stsepelin/zeppl/docs/reference/J1850-BUS.md

# J1850 bus reference — pinout, decode table, IM simulation

Reference for the V-Rod's SAE J1850 VPW bus: the 12-pin connector map, the
decoded message table (calibrated against real captures), the IM-simulation
protocol, and CRC. Status and roadmap live in [`../ROADMAP.md`](../ROADMAP.md);
the transceiver circuit + build live in [`HARDWARE.md`](HARDWARE.md).

## V-Rod instrument module 12-pin connector pinout

> Physical face map for building a mating quick-connect (cavity positions +
> wire colours): [`../schematics/im_connector_face.svg`](../schematics/im_connector_face.svg).
> Connector is a **Deutsch DTM06-12S** socket (molded marking); the bottom row
> numbering is **inverted** (12,11,10,9,8,7 left→right), verified on the bike.

| Pin | Wire Color | Signal | Type | T-tap Color | ESP32-P4 Connection |
|---|---|---|---|---|---|
| 1 | R/O (Red/Orange) | +12V Battery (constant) | Power | **Blue** | NOT used for cluster power (constant → would drain the battery key-off); switched pin 6 is the source instead |
| 2 | White | High Beam | 12V discrete | Red | → Voltage divider → GPIO input |
| 3 | Violet | Left Turn signal | 12V discrete | Red | → Voltage divider → GPIO input |
| 4 | Brown | Right Turn signal | 12V discrete | Red | → Voltage divider → GPIO input |
| 5 | BK/GN (Black/Green) | Ground | Power | **Blue** | → Common GND |
| 6 | Grey | +12V Ignition (switched) | Power | **Blue** | **cluster power source.** Full path (split point S2): pin 6 → **F1 2A inline in the harness** → signal board terminal (1,3) → row-1 rail (Q2's emitter taps off here) → transit (18,2) → power board → D2 → TVS1 → Mini560 → D4 → board 5V header. The signal board is upstream of D2, so it is fused but **not** reverse-protected. See [`../../firmware/docs/reference/bike-power-injection.md`](../../firmware/docs/reference/bike-power-injection.md) and [`../schematics/bike-power-chain.py`](../schematics/bike-power-chain.py). **⚠ Pin-6 conflict, OPEN:** this same pin is also listed as the sixth divider input (lane G6 "ignition"). Since pin 6 powers the board, G6 can only ever read "on". Options are laid out in [`../phases/phase3-cluster.md`](../phases/phase3-cluster.md); not yet decided. |
| 7 | LGN/V (Light Green/Violet) | **J1850 Data Bus** | Digital bus | Red | → DIY transceiver (RX + TX) |
| 8 | (3-pin sub-connector) | Vehicle Speed Sensor | Pulse | Red | → GPIO input (pulse counter) |
| 9 | GN/Y (Green/Yellow) | Oil Pressure warning | 12V discrete | Red | → Voltage divider → GPIO input |
| 10 | TN (Tan) | Neutral indicator | 12V discrete | Red | → Voltage divider → GPIO input |
| 11 | Y/W (Yellow/White) | Fuel Level sender | Analog resistance (see note) | Red | → ADC pin (GPIO 22 reserved) |
| 12 | O/W (Orange/White) | Accessories | 12V accessory | Red | → Optional |

Discrete-signal polarity (which lines are active-high vs active-low) and the
ultrasonic fuel-sender caveat are in the Phase 3 section of
[`../ROADMAP.md`](../ROADMAP.md).

## IM (instrument module) simulation

### Why it's needed
The V-Rod ECM expects the stock IM to respond on the J1850 bus. Without it:
U1255 DTC (missing response), possible TSSM security lockout.

### How it works
The P4 firmware periodically sends the same J1850 messages the stock IM sends,
via the high-side transceiver (IRLZ44N low-side driver → 2N2907A PNP sourcing
the bus HIGH for dominant). The ECM sees a "live" IM and stays happy.

> **Status (2026-07-24): Steps 1-3 done, on-bike validated.** Capture (Step 1)
> and Replay (Step 2) are live: the fabricated PCB keys the IM keep-alive set on
> the real bus with **0 watchdog faults over 312 sends** (engine-off/on +
> cold-start), stock cluster still attached, **no DTCs** (ROADMAP Phase 2
> Stage 4 + [`../../firmware/docs/rides/stage4-tx-bench-log.md`](../../firmware/docs/rides/stage4-tx-bench-log.md)).
> Step 3's stock-cluster **removal** / U1255 / TSSM checks are the open follow-up.

### Implementation steps

**Step 1 — Capture.** Proxy box passes everything to the stock cluster; log ALL
J1850 traffic for 5+ minutes (ignition on, engine running, riding); filter for
the messages the IM SENDS (not the ECM); document bytes, intervals, CRC.

**Step 2 — Replay.** Program the P4 to send the captured IM messages at the
right intervals via the TX circuit; VPW bit timing via RMT (64/128 µs pulses).

**Step 3 — Test.** Disconnect the stock cluster from the proxy output; run the
IM-simulation firmware; check for U1255 or any other DTCs; test key fob unlock →
start → ride → stop.

**Step 4 — Security handshake (if needed).** If TSSM security fails without the
stock IM: (A) capture + replay the security handshake (complex); (B) Screamin'
Eagle Pro tuner → disable TSSM; (C) keep the stock IM wired in parallel, hidden
under the airbox (fallback).

### CRC
J1850 VPW uses CRC-8 with polynomial 0x1D (CRC-8/SAE-J1850). Implemented in
`firmware/main/engine/j1850/j1850_vpw.c` (host-tested, round-tripped).

## J1850 VPW message decode table

Calibrated against real on-bike captures. The decoder is
`firmware/main/engine/j1850/j1850_parse.c` (host-tested); the DTC codec is `dtc.c`.

```
HEADER             DATA          MEANING
28 1B 10 02 HH LL  HH LL        RPM = (HH<<8 | LL) / 4
48 29 10 02 HH LL  HH LL        Speed: km/h-native raw counts (~117
                                 counts/km-h). speed_mph = speed_raw / 188
                                 (LOCKED Ride 2 — physics + radar, PR #27).
                                 The old /128 was an early bad guess.
48 3B 40 XX         XX           TSSM lever/shift EVENT frame (edge-driven, not
                                 periodic). Mapped in the stationary bike
                                 session 2026-07-24 (one-lever-at-a-time):
                                   bit7 (0x80) = CLUTCH  (toggles with the lever)
                                   bit5 (0x20) = GEAR-SHIFT event (shifter moved)
                                   bit1 (0x02) = clutch-idle / heartbeat marker
                                 Front brake and neutral are NOT on the bus —
                                 both are discrete (brake = lamp switch; neutral
                                 = pin-10 tap, active-low, Ph.6). SUPERSEDES the
                                 earlier "bit5 = brake / bit7 = heartbeat" guess
                                 (that bit5 was the clutch/shift, not the brake).
48 DA 40 39 XX      XX           Turn signals: bitfield, 3=both. On the
                                 2009 VRSCF (verified 2026-07-04):
                                 2=LEFT, 1=RIGHT (swapped vs HarleyDroid)
68 88 10 03         —            Check Engine OFF
68 88 10 83         —            Check Engine ON
A8 3B 10 03 XX      XX           ECM engine-load/throttle (function 3B), NOT
                                 gear (disproven Ride 1). Gear is DERIVED:
                                 argmin |rpm/speed - ratio| over the exact
                                 overall ratios; ~91% correct at divisor 188.
A8 49 10 10 XX      XX           Engine temp: °C = raw - 40 (OBD-style offset).
                                 Confirmed Ride 1: 0x3F(63)=23°C cold,
                                 0x81(129)=89°C warm. (No-offset read 40°C high.)
A8 69 10 06 HH LL  HH LL        Odometer: 1 tick = 0.4 meters
A8 83 10 0A HH LL  HH LL        Fuel consumption ticks: ~0.000309 L/tick
                                 (ml_per_tick=0.309, calibrated Ride 2 fill-up;
                                 supersedes the 0.000040 placeholder). Economy/range.
A8 83 61 12 DX      DX           Fuel gauge 0-6 — IM-ORIGINATED. Fuel LEVEL +
                                 low-fuel are NOT bus-decoded and likely
                                 disappear with the stock IM.
48 92 40 XX YY YY   XX YY YY     IMMOBILISER / security "key" lamp (CONFIRMED
68 93 60 XX YY YY   XX YY YY     on-bike 2026-07-24; decoded in j1850_parse.c ->
                                 the P4 key icon, verified against the stock
                                 cluster). Paired 40/60 sources. At key-on:
                                 data[3]=0xAA ("AA FF FF", not authenticated ->
                                 key lamp ON) for ~4 s, then data[3]=0x2A
                                 ("2A 00 00", authenticated -> lamp OFF).
                                 State bit = data[3] bit7. 48 92 40 is used.
28 FF 10 01 XX      XX           STATUS bitfield. bit0 (0x01) = KILL SWITCH
                                 (1 = STOP, 0 = RUN) — CONFIRMED on-bike
                                 2026-07-24 by toggling the run/stop switch
                                 (0x07<->0x06). Bits 1-2 stay set while
                                 stationary (engine off AND idling) — not oil;
                                 likely clear only when moving (ABS/road status),
                                 untested on the stand. OIL PRESSURE is NOT on
                                 the bus (it's the discrete pin-9 tap, Ph.6).
                                 Left undecoded (no kill-switch cluster icon).
```

Still-undecoded headers are catalogued in
[`../../firmware/docs/reference/j1850-undecoded-frames.md`](../../firmware/docs/reference/j1850-undecoded-frames.md).

### Diagnostic trouble codes (DTCs)
The HD J1850 read/clear protocol (request/response bytes, per-module addresses)
and the on-bike validation are in
[`../../firmware/docs/reference/dtc-read-probe.md`](../../firmware/docs/reference/dtc-read-probe.md);
the codec is `firmware/main/engine/j1850/dtc.c` (host-tested).
