stsepelin/zeppl/firmware/docs/captures/SESSION-2026-07-04.md

# J1850 capture session — 2026-07-04 (first live bike sniff)

2009 VRSCF Muscle, RX-only sniffer through the proxy box, stock cluster
in place. First on-bike Stage 2 session.

> **RESOLVED (2026-07-04): the bus is standard VPW; there is no
> inversion.** The `RX_INVERT` flag was masking the 500 ns hardware
> glitch filter, which dropped the slow recessive (dominant->idle)
> falling edge. Three independent sources agree the bus idles LOW /
> dominant HIGH: (1) bare-bus DMM (ESP disconnected) reads idle ~0.3 V;
> (2) an invert-off raw dump on short leads shows `raw1 low 41 s` (idle
> LOW) then `raw2 HIGH 194 us` (SOF HIGH); (3) with the glitch filter
> off, decode is clean WITHOUT the invert flag — same-level=0, 0 bad
> CRC, the best capture yet. `RX_INVERT` and the low-side TX have both
> been removed. **TX is HIGH-side** (original `j1850_tx.svg`, PNP +
> 2N2907A). See the glitch-window sweep below.

## Root cause: the glitch filter ate the recessive edge (not inversion)

Pulse widths came back textbook VPW (64 / 128 / 200 us) but the decoder
saw 0 frames with correct polarity, and only decoded with
`CONFIG_VROD_J1850_RX_INVERT=y`. That was first read as bus inversion;
the bare-bus DMM (idle LOW) contradicted it. The real cause: the P4
hardware flex glitch filter delays the filtered edge relative to the
ISR's `gpio_get_level()` read, so the recessive falling edge is
recorded at the wrong level — it shows up as over-long HIGH pulses that
break frames and make idle gaps look HIGH. Under invert those long-HIGH
glitches became passive pulses that ended frames cleanly, which is why
the flag "worked."

**Glitch-window sweep (engine running, idle + throttle blips, 6 passes):**

| filter window | frames decoded | bad CRC |
|---|---|---|
| **0 ns (off)** | **125 / 208 / 213 per 9 s** | **0** |
| 400 ns | 0 | — |
| 800 ns | 0 | — |
| 1200 ns | 0 | — |
| 1600 ns | 0 | — |

Only the filter-off window decodes — a hard cliff, not a gradient (400 ns
breaks it as completely as 1600 ns), which is the signature of the
edge-vs-level-read delay, not slow-edge eating. The P4 flex filter also
tops out at 1600 ns (64-tick field on the 40 MHz XTAL; 800 ns on the
default 80 MHz clock), so the 1-5 us some notes imagined was never
reachable. **Tuned default: `CONFIG_VROD_J1850_GLITCH_NS=0`.** Real
noise immunity for the Phase 3 permanent build must come from RX
hysteresis (a comparator front end), not this filter. A candidate ISR
fix — infer the level by toggling instead of reading the pin — would
sidestep the delay race and let a filter coexist; deferred, not yet
tried.

## Captures

| File | Bike state | Notes |
|---|---|---|
| `2026-07-04-inverted.log` | key ON, engine OFF, **neutral**, **high-beam bulb removed**, signals off, stationary | ignition-on baseline; also contains the inversion-discovery raw pulse dump at the top. ~232 frames, ~3% bad CRC. |

## Ignition-on baseline (engine off) — what broadcasts

Bus is sparse at key-on; only these repeat, ~2 s cadence:

- `29 FE 40 ..` / `29 FE 60 ..`  — steady pair
- `68 FF 40 03 D8` / `68 FF 60 03 AD` — steady pair

None match our ECM-oriented decode table (`28 1B`, `48 29`, `A8 ..`) —
these are **IM-originated keep-alive**, the Stage 4 replay candidates.

One-shots seen at power-up: `48 92 40 2A`, `68 93 60 2A`, `29 81 60`,
`68 E0 B0`, and one `48 DA 40 39 00 70` (turn-signal header, value 00 =
off — matches the decode table).

Remember: this baseline has **neutral = engaged** and **beam bulb out**
baked in. Anything that reads those states is at its neutral/beam-off
value here.

## Decoded so far (engine off)

**Turn signals — `48 DA 40 39 XX`** (via TSSM, a bus node). `XX` is a
2-bit field, blinks between the value and `00`:

| XX | meaning | CRC byte |
|----|---|---|
| 00 | off | 70 |
| 02 | **left** | 4A |
| 01 | **right** | 6D |
| 03 | both / hazards (= 01\|02) | 57 |

Note: **left/right are swapped vs the HarleyDroid table** (it says
1=left, 2=right; this bike is 2=left, 1=right). Verified by test order
(left tested first → 02). Our CRC-8 matched every frame.

**Beam, neutral, oil are NOT on the bus.** Toggling high beam and
shifting out of neutral produced zero change in J1850 traffic. On the
V-Rod these are **discrete 12 V wires to the IM** — pin 2 White = high
beam, pin 10 Tan = neutral, pin 9 GN/Y = oil pressure — read locally by
the IM, not broadcast. We tap them directly via voltage dividers in
Phase 3. (Oil light ON at engine-off is normal: no oil pressure with
the engine stopped → pressure switch closed → lamp on; it extinguishes
once the engine builds pressure. Confirms the oil signal works.)

## Decoded — engine running (kill switch RUN woke the ECM)

All validated against live behaviour:

- **RPM — `28 1B 10 02 HH LL`**, `(HH<<8|LL)/4`. Confirmed: idle ~1300,
  tracked a clean sustained rev to **4125 rpm** and back, sampled ~15/s
  (66 ms interval, fast enough to drive a tach). Session max 4684.
- **Engine temp — `A8 49 10 10 XX`** — **units UNRESOLVED, PROVISIONAL.**
  The raw byte climbed `0x3E..0x48` (62..72) as it warmed, but the **stock
  cluster shows NO temperature**, so there is no dial to validate against —
  the earlier "raw = °C" was a plausibility guess, not confirmed. Three
  candidates all fit the observed climb: raw°C (62..72°C), raw°F (~17..22°C),
  or `raw-40=°C` (22..32°C). HarleyDroid's wiki documents `xx = °C + 40`
  (i.e. `raw-40`), with a conflicting source saying °F — a HINT only (its
  turn-signal bits were wrong too). **Resolve with a two-point capture**
  (below): raw byte at cold (~ambient) and fully warm (~90-100°C) fixes
  scale + offset unambiguously. The firmware keeps raw-as-°C provisionally
  and logs the raw byte (`temp:` line).
- **Gear — `A8 3B 10 03 XX`**, `00` = neutral (bits 1,3,7,15,31,63 →
  gears 1-6 per table; only neutral seen on the stand).
- **Check engine — `68 88 10 03`** = OFF (0x83 would be ON).
- **Fuel consumption — `A8 83 10 0A HH LL`** present (88 frames, ever-
  incrementing counter) — this is the tick stream for the fuel-computer
  fallback to the ultrasonic sender (see roadmap Phase 3 caveat).
- **Speed — `48 29 10 02`** header confirmed present (reads 0 on the
  stand). **Units settled: mph-native** — this is a US-market bike, the
  stock cluster reads miles, so the ECM value is mph-based; km/h is a
  DISPLAY-layer conversion, not decode. `vehicle_data.speed_mph` is now
  mph-canonical (the sim producer converts to mph; the display does
  mph→km/h only in metric mode). **Magnitude still provisional**: the
  `/DIV` scale (128 guess) needs a ride — the firmware logs the native
  decoded speed (`speed:` line) to compare against the stock speedometer
  read in its native miles (mechanically driven off this same bus).

## IM keep-alive set (Stage 4 replay candidates)

Steady ~2 s cadence, single payload, present with the stock cluster
connected — the messages the P4 must emit to impersonate the IM:

| Header | payload | interval |
|---|---|---|
| `68 FF 40` | `03 D8` | ~2.0 s |
| `68 FF 60` | `03 AD` | ~2.0 s |
| `29 FE 40` | `01 64` | ~2.0 s |
| `29 FE 60` | `01 11` | ~2.0 s |

(Plus `C8 88 10`, `C8 89 60`, `E8 89 60`, `68 FF 10` — ECM/diagnostic
broadcasts, ~2-6 s. Confirm which are IM- vs ECM-originated by watching
what disappears when the stock cluster is unplugged — that's a Stage 4
test, not done yet.)

Overall: 5177 frames across all captures, ~2% bad CRC (healthy, even at
5k rpm). Full breakdown: `tools/j1850_report.py firmware/docs/captures/*.log`.

## Ride / engine session agenda (next, done safely)

> These captures now run **laptop-free**: build with `CONFIG_VROD_RIDE_LOG=y`,
> hit REC on the BENCH screen, ride, hit STOP, then power off and pull the
> microSD card. The log persists native speed, the raw temp byte, and gear
> raw+decoded per frame (see Stage 3.5 in the Phase 2 plan). Needs the ESP on
> bike power (switched +12V via the buck), NOT USB. Run
> `tools/j1850_report.py /sdcard/ride_NNN.log` afterward.

- **Road speed** `48 29 10 02` — units settled (mph-native); confirm the
  `/DIV` magnitude by comparing the logged native speed (`speed:` line)
  against the STOCK SPEEDOMETER read in its native miles (ignore the km/h
  sticker — the mechanism reads mph) at steady 30 / 50 / 70. The stock
  speedo may read ~5-10% optimistic, so this is a coarse check; correct
  DIV if off by a clean factor. (No onboard GPS.)
- **All six gears** `A8 3B 10 03 XX` — only neutral (00) seen parked;
  shift up through the box to log 1st-6th and confirm the table's
  `1,3,7,15,31,63` per-gear values.
- **Two-point temperature** `A8 49 10 10` — record the RAW byte
  (`temp:` line) at TWO known temps: (1) cold engine sat overnight ≈
  ambient (note the ambient), (2) fully warmed ≈ 90-100 °C. Two points fix
  scale AND offset, choosing between raw°C / raw°F / `raw-40=°C`. No dial
  reference exists (stock cluster shows no temp), so this capture is the
  only way to resolve it.
- Anything else speed-dependent we haven't seen at rest.

## Other open items
- **Bus polarity + TX topology — RESOLVED (see the banner at the top).**
  Standard VPW, idle LOW (~0 V), dominant HIGH (~7 V) → **high-side TX**
  (original `j1850_tx.svg`, PNP + 2N2907A). `RX_INVERT` and the low-side
  `j1850_transceiver.svg` are removed. The old "inversion" was the
  500 ns glitch filter dropping the recessive edge; filter now defaults
  off (`CONFIG_VROD_J1850_GLITCH_NS=0`).
- **RX noise immunity (Phase 3):** with the hardware filter unusable,
  vibration/ignition-noise rejection on the permanent harness needs RX
  hysteresis (comparator front end). Optionally revisit the toggle-based
  ISR level capture, which would let a small filter coexist.
- **IM- vs ECM-originated split** — confirm by unplugging the stock
  cluster and seeing which keep-alives vanish (Stage 4).
