stsepelin/zeppl/docs/adr/README.md

# Architecture Decision Records

Short, dated records of significant architecture decisions — the *why* behind a
structural direction, kept next to the code so the reasoning survives. One file
per decision, numbered.

| # | Decision | Status |
|---|---|---|
| [0001](0001-engine-display-split.md) | Engine / connectivity / display separation (contract-first; CAN+DBC interop; defer the board split) | Proposed |

New ADR: copy the shape of an existing one — context, decision, consequences,
and (if it implies work) a phased plan + open questions.
