stsepelin/zeppl/firmware/main/assets/boot.gif

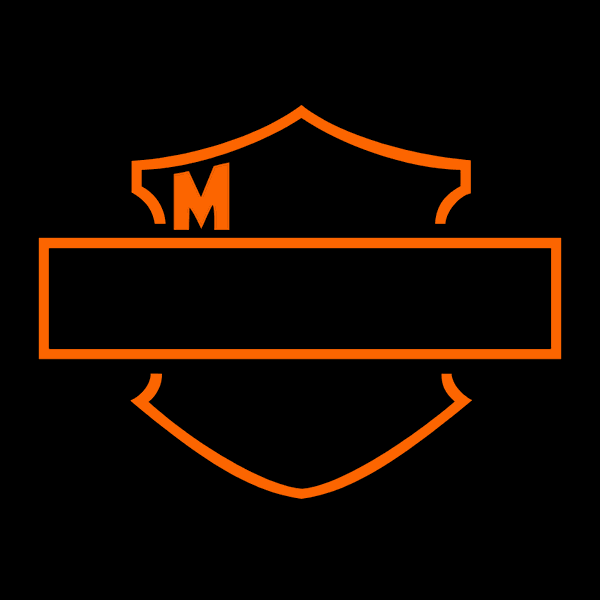
firmware/main/assets/boot.gif
