stsepelin/zeppl/hardware/enclosure/bezel.png

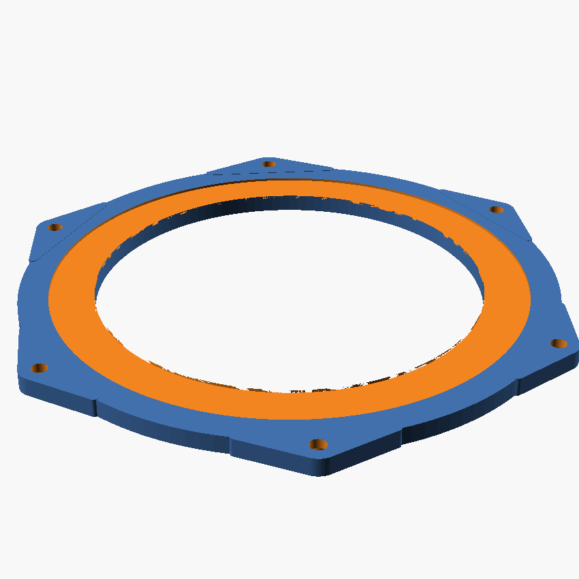
hardware/enclosure/bezel.png
