stsepelin/zeppl/hardware/enclosure/bezel_ear_closeup.png

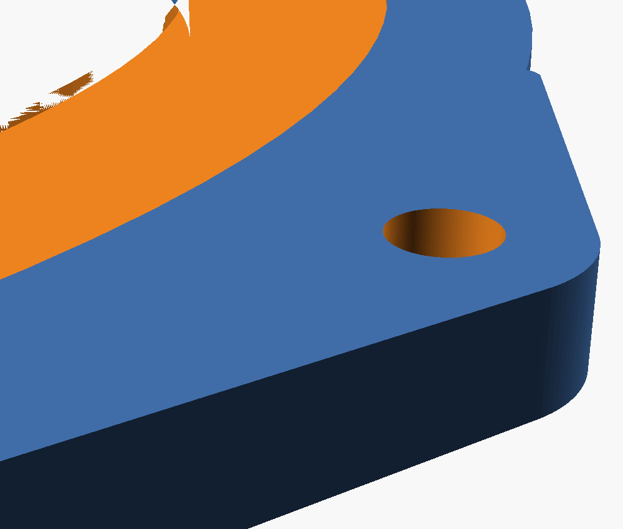
hardware/enclosure/bezel_ear_closeup.png
