stsepelin/zeppl/hardware/enclosure/cable_hole_view.png

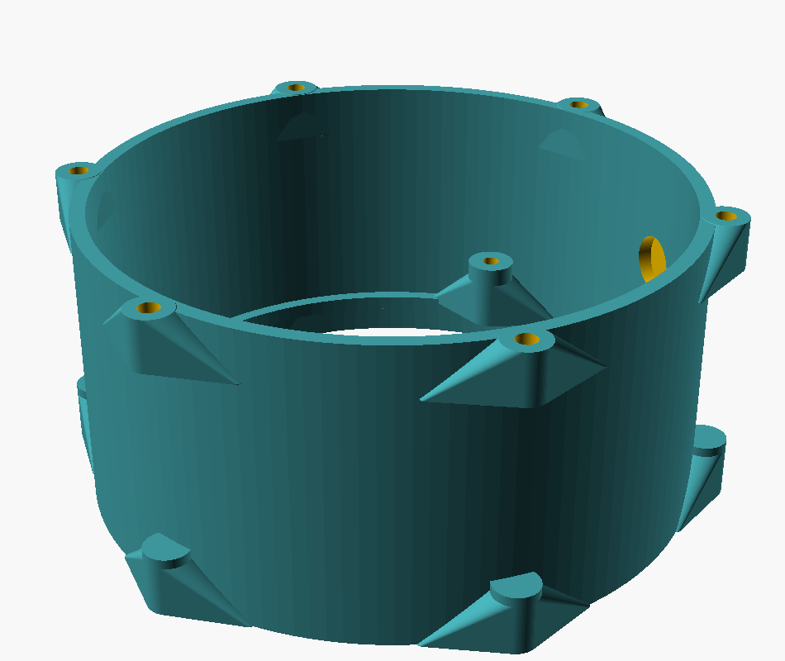
hardware/enclosure/cable_hole_view.png
