stsepelin/zeppl/hardware/enclosure/perimeter_boss_closeup.png

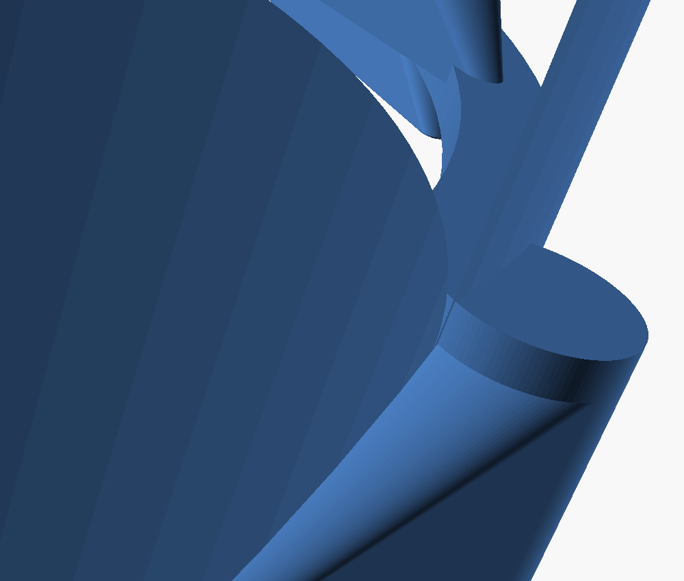
hardware/enclosure/perimeter_boss_closeup.png
