stsepelin/zeppl/hardware/enclosure/rear_case.png

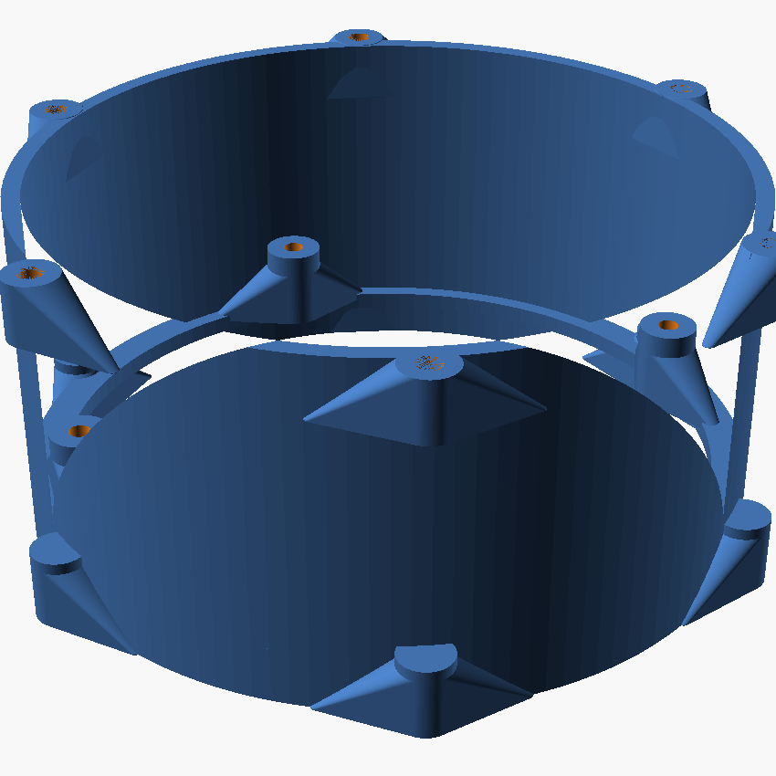
hardware/enclosure/rear_case.png
