stsepelin/zeppl/hardware/enclosure/rear_cover.png

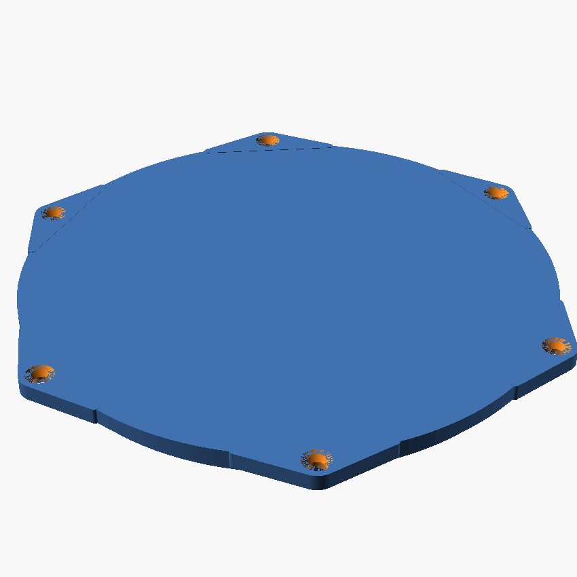
hardware/enclosure/rear_cover.png
