stsepelin/zeppl/hardware/enclosure/section.png

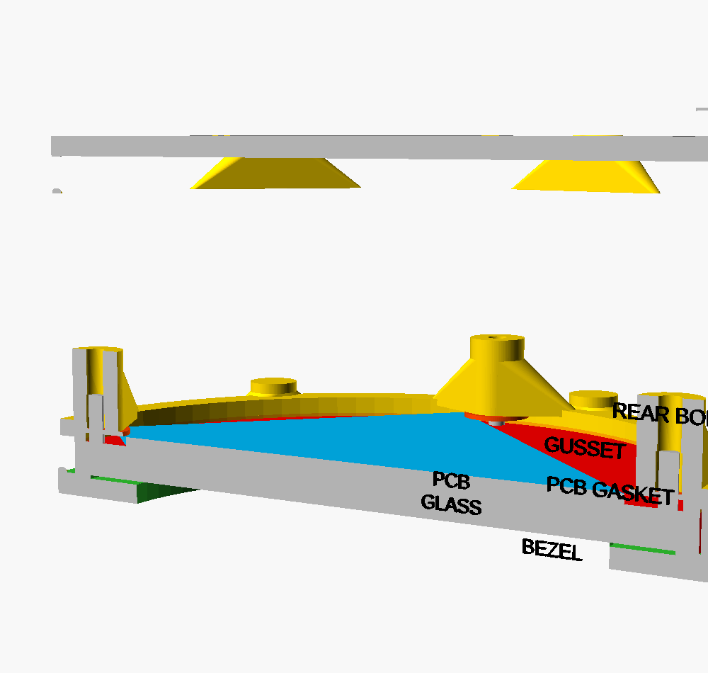
hardware/enclosure/section.png
