stsepelin/zeppl/hardware/enclosure/standoff_closeup.png

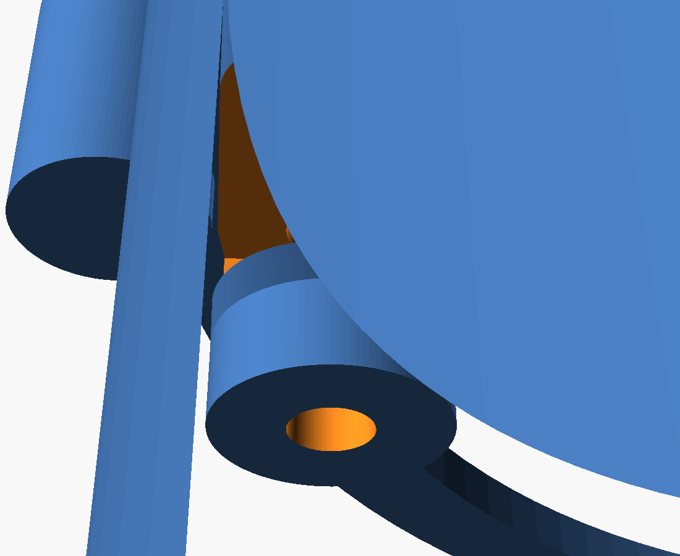
hardware/enclosure/standoff_closeup.png
