stsepelin/zeppl/hardware/enclosure/assembly.png

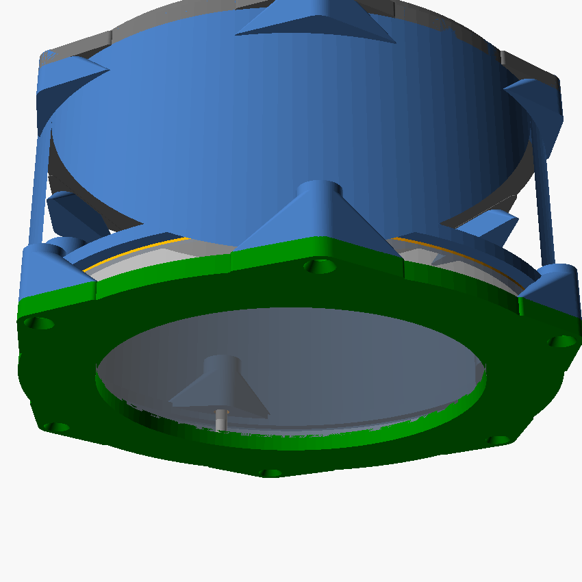
hardware/enclosure/assembly.png
