stsepelin/zeppl/hardware/enclosure/calibration_base.png

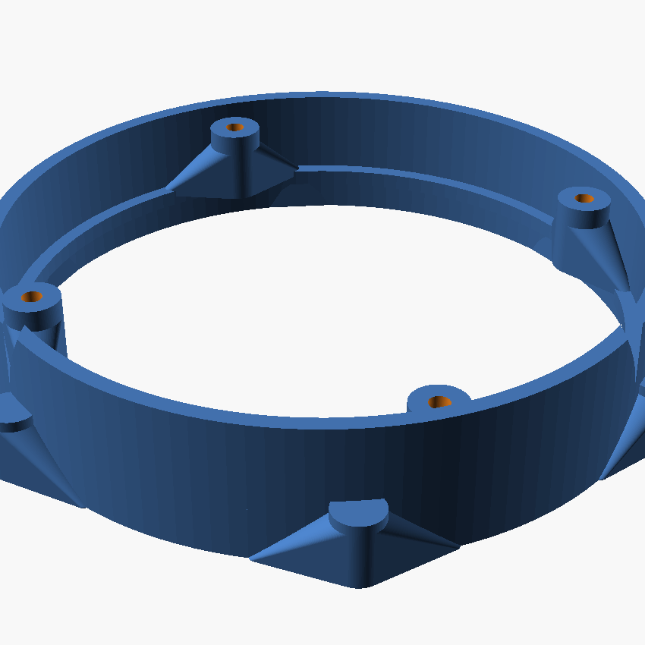
hardware/enclosure/calibration_base.png
