stsepelin/zeppl/firmware/main/display/format.h

#pragma once
#include <stdint.h>
#include <stddef.h>

// Pure-C numeric formatters used by the readout widgets. Extracted so they
// can be unit-tested on a host build without dragging LVGL into the picture.

// Writes `value` as a thousand-separated decimal into `out`, e.g.:
//   0        -> "0"
//   123      -> "123"
//   12847    -> "12,847"
//   1234567  -> "1,234,567"
// `out_size` must be >= 15 (enough for any uint32_t).
void format_km_grouped(uint32_t value, char *out, size_t out_size);

// Copies `in` into `out`, truncated to at most `max_cp` UTF-8 codepoints
// (counted per character, not per byte, so multi-byte text isn't cut in
// half) and appends "..." when truncation happened. Never writes more
// than out_size bytes including the NUL.
void format_truncate_utf8(char *out, size_t out_size, const char *in, size_t max_cp);
