stsepelin/zeppl/firmware/docs/waveshare-reference/examples/esp-idf/08_lvgl_demo_v9/main/main.c

#include "lvgl.h"
#include "bsp/esp-bsp.h"
#include "bsp/display.h"
#include "lv_demos.h"

void app_main(void)
{

/*
If you need to use the three-cache anti-tear configuration, you need to fix idf 5.5. Refer to: https://github.com/espressif/esp-iot-solution/blob/da973d162cc88736a4e05e6582393e666f221c2a/components/display/tools/esp_lvgl_adapter/README.md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 
*/
    bsp_display_cfg_t cfg = {
        .lv_adapter_cfg = ESP_LV_ADAPTER_DEFAULT_CONFIG(),
        .rotation = ESP_LV_ADAPTER_ROTATE_0,
        .tear_avoid_mode = ESP_LV_ADAPTER_TEAR_AVOID_MODE_TRIPLE_PARTIAL,
        .touch_flags = {
            .swap_xy = 0,
            .mirror_x = 0,
            .mirror_y = 0
        }};
    bsp_display_start_with_config(&cfg);
    bsp_display_backlight_on();

    bsp_display_lock(-1);

    // lv_demo_music();
    // lv_demo_benchmark();
    lv_demo_widgets();

    bsp_display_unlock();
}
